AymanTarek2/Spider-Robot/Spider Solidworks/Spider Robot stl/Link2 x4 .STL

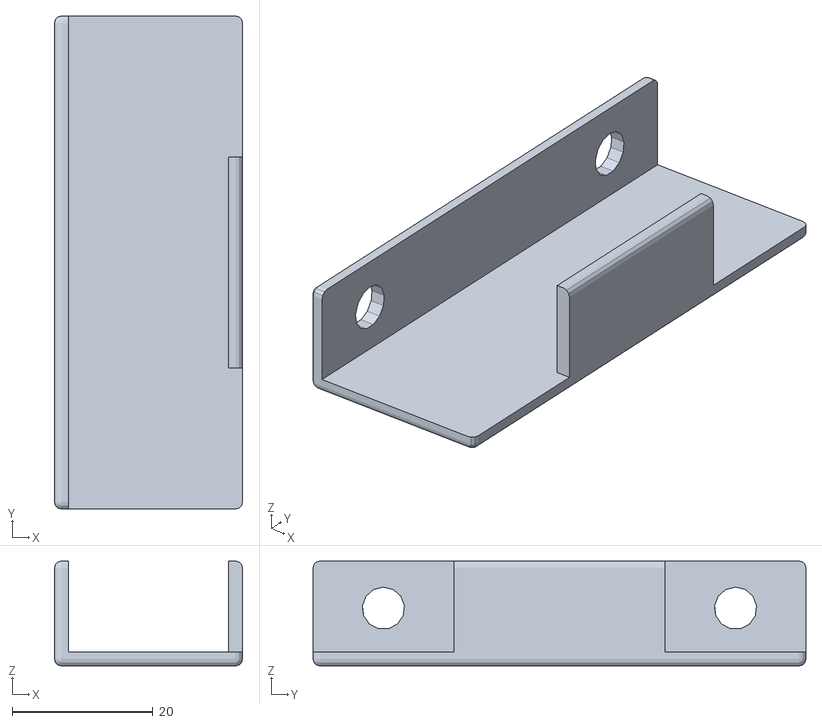
[picture p15: CAD file, 2026-06-20]
Spider Solidworks/Spider Robot stl/Link2 x4 .STL
26.7 x 70.0 x 14.9
