AymanTarek2/Spider-Robot/Spider Solidworks/Spider Head.SLDPRT

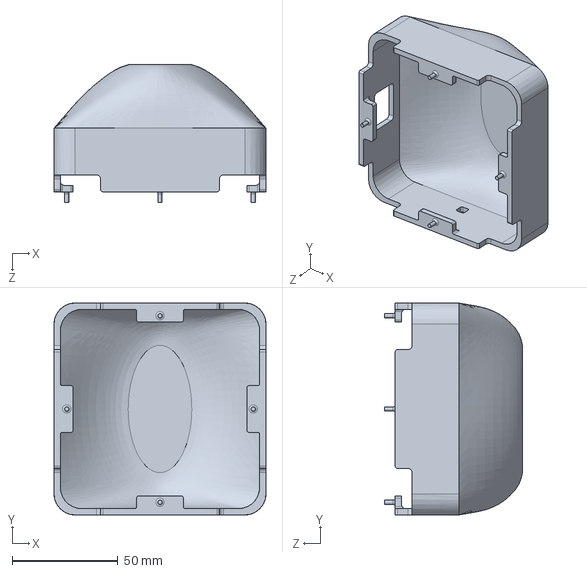
[picture p16: CAD file, 2026-06-20]
Spider Solidworks/Spider Head.SLDPRT
100.0 x 100.0 x 65.0 mm
