AymanTarek2/Spider-Robot/Spider Solidworks/Spider Robot stl 2/spider 3d print #2/link3.STL

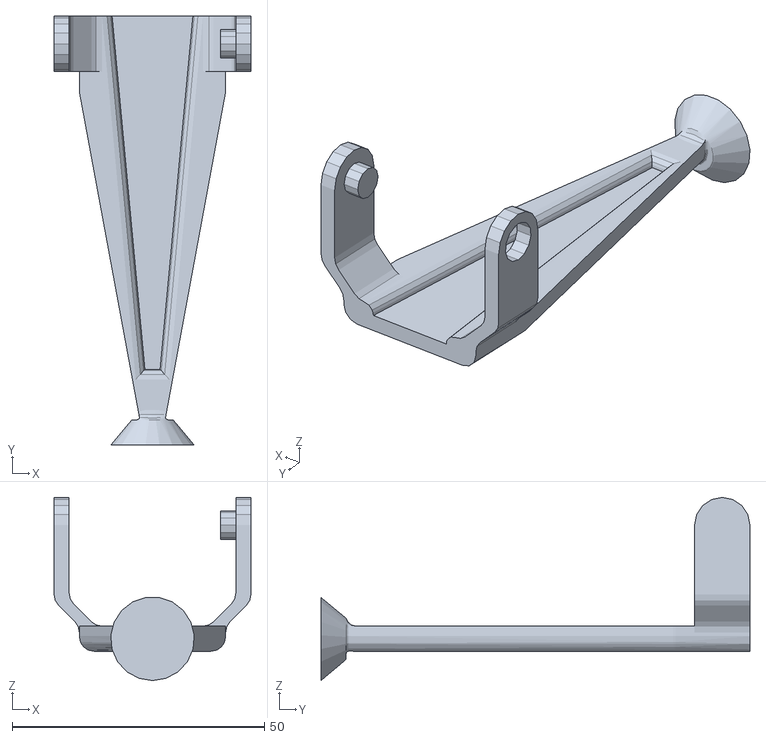
[picture p17: CAD file, 2026-06-20]
Spider Solidworks/Spider Robot stl 2/spider 3d print #2/link3.STL
39.0 x 85.0 x 36.3
