AymanTarek2/Spider-Robot/Spider Solidworks/Spider Robot stl/Link1 x4 .STL

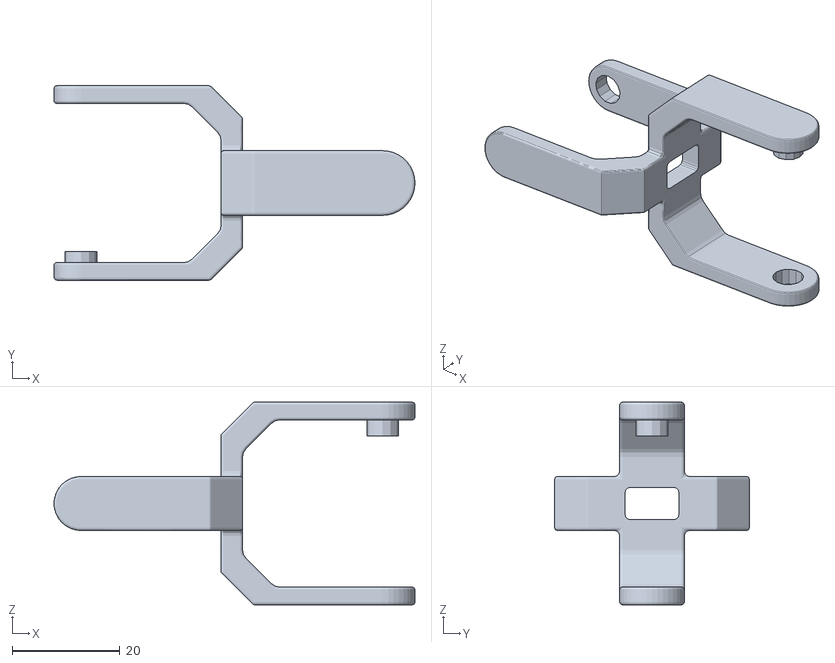
[picture p18: CAD file, 2026-06-20]
Spider Solidworks/Spider Robot stl/Link1 x4 .STL
67.0 x 36.1 x 37.6
