AymanTarek2/Spider-Robot/Spider Solidworks/Body.SLDPRT

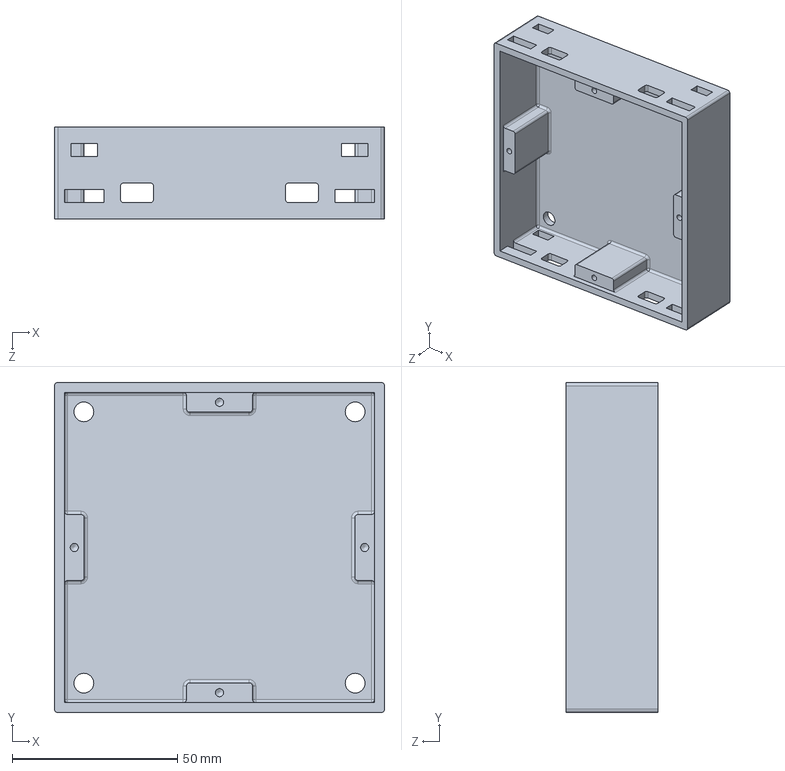
[picture p19: CAD file, 2026-06-20]
Spider Solidworks/Body.SLDPRT
100.0 x 100.0 x 28.0 mm
