AymanTarek2/Spider-Robot/Spider Solidworks/Spider Robot stl/Link3 x4 .STL

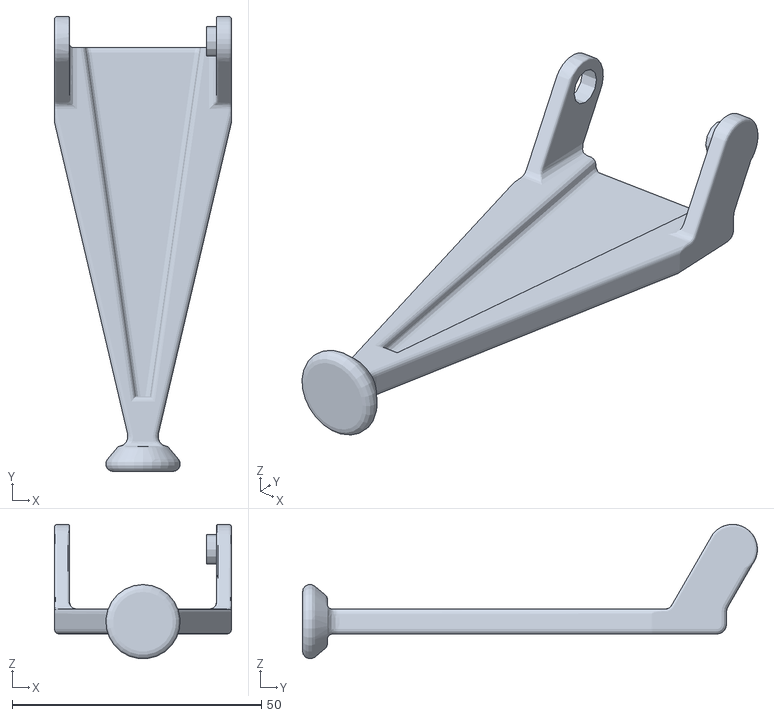
[picture p20: CAD file, 2026-06-20]
Spider Solidworks/Spider Robot stl/Link3 x4 .STL
35.5 x 91.2 x 26.9
