AymanTarek2/Spider-Robot/Spider Solidworks/User Library-Servo9G.sldprt

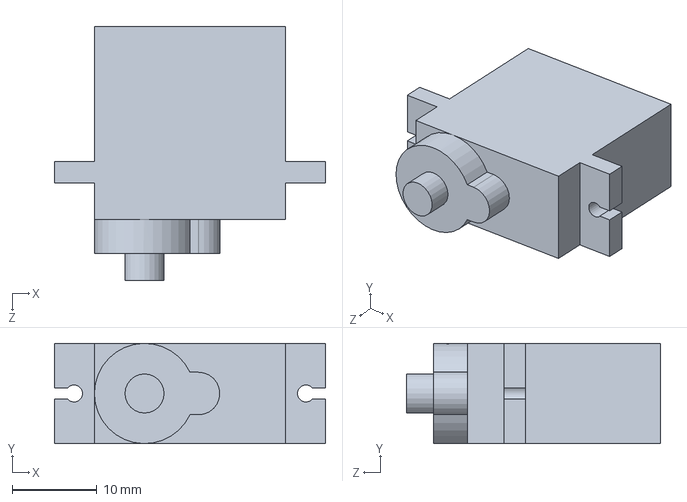
[picture p21: CAD file, 2026-06-20]
Spider Solidworks/User Library-Servo9G.sldprt
31.9 x 11.8 x 29.9 mm
